opyh/liftsensor/firmware/electron/firmware/CellLocation.h

/******************************************************************************
  Copyright (c) 2015 Particle Industries, Inc.  All rights reserved.

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
  You should have received a copy of the GNU Lesser General Public
  License along with this program; if not, see <http://www.gnu.org/licenses/>.
 ******************************************************************************/

#ifndef CELL_LOCATION_H
#define CELL_LOCATION_H


#include "application.h"
#include "cellular_hal.h"

class CellLocation {
  struct MDM_CELL_LOCATE {
    int day;
    int month;
    int year;
    int hour;
    int minute;
    int second;
    char lat[14];
    char lng[14];
    int altitude; // only for GNSS positioning
    int uncertainty;
    int speed; // only for GNSS positioning
    int direction; // only for GNSS positioning
    int vertical_acc; // only for GNSS positioning
    int sensor_used; // 0: the last fix in the internal database, 2: CellLocate(R) location information
    int sv_used; // only for GNSS positioning
    int antenna_status; // only for GNSS positioning
    int jamming_status; // only for GNSS positioning
    int count;
    bool ok;
    int size;

    MDM_CELL_LOCATE() {
      memset(this, 0, sizeof(*this));
      size = sizeof(*this);
    }
  };

  static MDM_CELL_LOCATE _cellLocate;
  static bool displayed_once;
  static volatile uint32_t cellTimeout;
  static volatile uint32_t cellTimeStart;

  static void setTimeout(uint32_t timeout_ms);
  static bool isTimedOut();
  static void clearTimeout();
  static int locateCallback(int type, const char* buf, int len, MDM_CELL_LOCATE* data);
  static int cellLocate(MDM_CELL_LOCATE& loc, uint32_t timeout_ms);
  static bool isInProgress(MDM_CELL_LOCATE& loc);
  static bool getResponse(MDM_CELL_LOCATE& loc);
  static void display(MDM_CELL_LOCATE& loc);

public:
  static void startLocating();
  static void reprogramAssistNowServer();
};

#endif
